greatscottgadgets/daisho/sw/fpga/common/usb3/usb3_crc.v

//
// usb 3.0 crc assortment
//
// Copyright (C) 2009 OutputLogic.com
// Reformatting / adaptation by Marshall H., 2013
// This source file may be used and distributed without restriction
// provided that this copyright statement is not removed from the file
// and that any derivative work contains the original copyright notice
// and the associated disclaimer.
//
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


//
// CRC-5 for Command Words, Link Control Word
//
module usb3_crc_cw(

input 	wire	[10:0] 	di,
output 	wire	[4:0] 	crc_out

);

// reverse input
wire	[10:0]	d = { 	di[0], di[1], di[2], di[3], di[4], 
						di[5], di[6], di[7], di[8], di[9], 
						di[10] };
wire	[4:0]	c = 5'h1F;						
wire	[4:0]	q = {	^d[10:9] ^ ^d[6:5] ^ d[3] ^ d[0] ^ c[0] ^ ^c[4:3],
						d[10] ^ ^d[7:6] ^ d[4] ^ d[1] ^ ^c[1:0] ^ c[4],
						^d[10:7] ^ d[6] ^ ^d[3:2] ^ d[0] ^ ^c[4:0],
						^d[10:7] ^^ d[4:3] ^ d[1] ^ ^c[4:1],
						^d[10:8] ^ ^d[5:4] ^ d[2] ^ ^c[4:2]	};
assign	crc_out = ~q;
	
endmodule



//
// CRC-16 for Header Packets
//
module usb3_crc_hp(

input	wire	[31:0] 	di,
input	wire			crc_en,
output	wire	[15:0] 	crc_out,
input	wire			rst,
input	wire			clk

);

reg [15:0]	q;
wire [15:0]	c;
wire [31:0] d = {	di[0 ],di[1 ],di[2 ],di[3 ],di[4 ],di[5 ],di[6 ],di[7],
					di[8 ],di[9 ],di[10],di[11],di[12],di[13],di[14],di[15],
					di[16],di[17],di[18],di[19],di[20],di[21],di[22],di[23],
					di[24],di[25],di[26],di[27],di[28],di[29],di[30],di[31]};
assign crc_out = ~{	q[0], q[1], q[2], q[3], q[4], q[5], q[6], q[7], 
					q[8], q[9], q[10],q[11],q[12],q[13],q[14],q[15]};

assign	c[0] = q[4] ^ q[5] ^ q[7] ^ q[10] ^ q[12] ^ q[13] ^ q[15] ^ d[0] ^ d[4] ^ d[8] ^ d[12] ^ d[13] ^ d[15] ^ d[20] ^ d[21] ^ d[23] ^ d[26] ^ d[28] ^ d[29] ^ d[31];
assign	c[1] = q[0] ^ q[4] ^ q[6] ^ q[7] ^ q[8] ^ q[10] ^ q[11] ^ q[12] ^ q[14] ^ q[15] ^ d[0] ^ d[1] ^ d[4] ^ d[5] ^ d[8] ^ d[9] ^ d[12] ^ d[14] ^ d[15] ^ d[16] ^ d[20] ^ d[22] ^ d[23] ^ d[24] ^ d[26] ^ d[27] ^ d[28] ^ d[30] ^ d[31];
assign	c[2] = q[0] ^ q[1] ^ q[5] ^ q[7] ^ q[8] ^ q[9] ^ q[11] ^ q[12] ^ q[13] ^ q[15] ^ d[1] ^ d[2] ^ d[5] ^ d[6] ^ d[9] ^ d[10] ^ d[13] ^ d[15] ^ d[16] ^ d[17] ^ d[21] ^ d[23] ^ d[24] ^ d[25] ^ d[27] ^ d[28] ^ d[29] ^ d[31];
assign	c[3] = q[0] ^ q[1] ^ q[2] ^ q[4] ^ q[5] ^ q[6] ^ q[7] ^ q[8] ^ q[9] ^ q[14] ^ q[15] ^ d[0] ^ d[2] ^ d[3] ^ d[4] ^ d[6] ^ d[7] ^ d[8] ^ d[10] ^ d[11] ^ d[12] ^ d[13] ^ d[14] ^ d[15] ^ d[16] ^ d[17] ^ d[18] ^ d[20] ^ d[21] ^ d[22] ^ d[23] ^ d[24] ^ d[25] ^ d[30] ^ d[31];
assign	c[4] = q[0] ^ q[1] ^ q[2] ^ q[3] ^ q[5] ^ q[6] ^ q[7] ^ q[8] ^ q[9] ^ q[10] ^ q[15] ^ d[1] ^ d[3] ^ d[4] ^ d[5] ^ d[7] ^ d[8] ^ d[9] ^ d[11] ^ d[12] ^ d[13] ^ d[14] ^ d[15] ^ d[16] ^ d[17] ^ d[18] ^ d[19] ^ d[21] ^ d[22] ^ d[23] ^ d[24] ^ d[25] ^ d[26] ^ d[31];
assign	c[5] = q[0] ^ q[1] ^ q[2] ^ q[3] ^ q[4] ^ q[6] ^ q[7] ^ q[8] ^ q[9] ^ q[10] ^ q[11] ^ d[2] ^ d[4] ^ d[5] ^ d[6] ^ d[8] ^ d[9] ^ d[10] ^ d[12] ^ d[13] ^ d[14] ^ d[15] ^ d[16] ^ d[17] ^ d[18] ^ d[19] ^ d[20] ^ d[22] ^ d[23] ^ d[24] ^ d[25] ^ d[26] ^ d[27];
assign	c[6] = q[0] ^ q[1] ^ q[2] ^ q[3] ^ q[4] ^ q[5] ^ q[7] ^ q[8] ^ q[9] ^ q[10] ^ q[11] ^ q[12] ^ d[3] ^ d[5] ^ d[6] ^ d[7] ^ d[9] ^ d[10] ^ d[11] ^ d[13] ^ d[14] ^ d[15] ^ d[16] ^ d[17] ^ d[18] ^ d[19] ^ d[20] ^ d[21] ^ d[23] ^ d[24] ^ d[25] ^ d[26] ^ d[27] ^ d[28];
assign	c[7] = q[0] ^ q[1] ^ q[2] ^ q[3] ^ q[4] ^ q[5] ^ q[6] ^ q[8] ^ q[9] ^ q[10] ^ q[11] ^ q[12] ^ q[13] ^ d[4] ^ d[6] ^ d[7] ^ d[8] ^ d[10] ^ d[11] ^ d[12] ^ d[14] ^ d[15] ^ d[16] ^ d[17] ^ d[18] ^ d[19] ^ d[20] ^ d[21] ^ d[22] ^ d[24] ^ d[25] ^ d[26] ^ d[27] ^ d[28] ^ d[29];
assign	c[8] = q[0] ^ q[1] ^ q[2] ^ q[3] ^ q[4] ^ q[5] ^ q[6] ^ q[7] ^ q[9] ^ q[10] ^ q[11] ^ q[12] ^ q[13] ^ q[14] ^ d[5] ^ d[7] ^ d[8] ^ d[9] ^ d[11] ^ d[12] ^ d[13] ^ d[15] ^ d[16] ^ d[17] ^ d[18] ^ d[19] ^ d[20] ^ d[21] ^ d[22] ^ d[23] ^ d[25] ^ d[26] ^ d[27] ^ d[28] ^ d[29] ^ d[30];
assign	c[9] = q[0] ^ q[1] ^ q[2] ^ q[3] ^ q[4] ^ q[5] ^ q[6] ^ q[7] ^ q[8] ^ q[10] ^ q[11] ^ q[12] ^ q[13] ^ q[14] ^ q[15] ^ d[6] ^ d[8] ^ d[9] ^ d[10] ^ d[12] ^ d[13] ^ d[14] ^ d[16] ^ d[17] ^ d[18] ^ d[19] ^ d[20] ^ d[21] ^ d[22] ^ d[23] ^ d[24] ^ d[26] ^ d[27] ^ d[28] ^ d[29] ^ d[30] ^ d[31];
assign	c[10] = q[1] ^ q[2] ^ q[3] ^ q[4] ^ q[5] ^ q[6] ^ q[7] ^ q[8] ^ q[9] ^ q[11] ^ q[12] ^ q[13] ^ q[14] ^ q[15] ^ d[7] ^ d[9] ^ d[10] ^ d[11] ^ d[13] ^ d[14] ^ d[15] ^ d[17] ^ d[18] ^ d[19] ^ d[20] ^ d[21] ^ d[22] ^ d[23] ^ d[24] ^ d[25] ^ d[27] ^ d[28] ^ d[29] ^ d[30] ^ d[31]; 
assign  c[11] = q[0] ^ q[2] ^ q[3] ^ q[4] ^ q[5] ^ q[6] ^ q[7] ^ q[8] ^ q[9] ^ q[10] ^ q[12] ^ q[13] ^ q[14] ^ q[15] ^ d[8] ^ d[10] ^ d[11] ^ d[12] ^ d[14] ^ d[15] ^ d[16] ^ d[18] ^ d[19] ^ d[20] ^ d[21] ^ d[22] ^ d[23] ^ d[24] ^ d[25] ^ d[26] ^ d[28] ^ d[29] ^ d[30] ^ d[31];
assign	c[12] = q[0] ^ q[1] ^ q[3] ^ q[6] ^ q[8] ^ q[9] ^ q[11] ^ q[12] ^ q[14] ^ d[0] ^ d[4] ^ d[8] ^ d[9] ^ d[11] ^ d[16] ^ d[17] ^ d[19] ^ d[22] ^ d[24] ^ d[25] ^ d[27] ^ d[28] ^ d[30];
assign	c[13] = q[1] ^ q[2] ^ q[4] ^ q[7] ^ q[9] ^ q[10] ^ q[12] ^ q[13] ^ q[15] ^ d[1] ^ d[5] ^ d[9] ^ d[10] ^ d[12] ^ d[17] ^ d[18] ^ d[20] ^ d[23] ^ d[25] ^ d[26] ^ d[28] ^ d[29] ^ d[31];
assign	c[14] = q[2] ^ q[3] ^ q[5] ^ q[8] ^ q[10] ^ q[11] ^ q[13] ^ q[14] ^ d[2] ^ d[6] ^ d[10] ^ d[11] ^ d[13] ^ d[18] ^ d[19] ^ d[21] ^ d[24] ^ d[26] ^ d[27] ^ d[29] ^ d[30];
assign	c[15] = q[3] ^ q[4] ^ q[6] ^ q[9] ^ q[11] ^ q[12] ^ q[14] ^ q[15] ^ d[3] ^ d[7] ^ d[11] ^ d[12] ^ d[14] ^ d[19] ^ d[20] ^ d[22] ^ d[25] ^ d[27] ^ d[28] ^ d[30] ^ d[31];

always @(posedge clk, posedge rst) begin
	if(rst) begin
		q <= {16{1'b1}};
	end
	else begin
		q <= crc_en ? c : q;
	end
end

endmodule



//
// CRC-32 for Data Packet Payloads
//
module usb3_crc_dpp32(

input 	wire	[31:0]	di,
output	wire	[31:0]	lfsr_q,
input 	wire			crc_en,
output	wire	[31:0]	crc_out,
input	wire			rst,
input	wire			clk

);

reg [31:0] q;

wire [31:0]	c;
wire [31:0] d = {	di[0 ],di[1 ],di[2 ],di[3 ],di[4 ],di[5 ],di[6 ],di[7],
					di[8 ],di[9 ],di[10],di[11],di[12],di[13],di[14],di[15],
					di[16],di[17],di[18],di[19],di[20],di[21],di[22],di[23],
					di[24],di[25],di[26],di[27],di[28],di[29],di[30],di[31]};
						
assign lfsr_q = q;
assign crc_out = ~{	q[0],  q[1],  q[2],  q[3],  q[4],  q[5],  q[6],  q[7], 
					q[8],  q[9],  q[10], q[11], q[12], q[13], q[14], q[15],
					q[16], q[17], q[18], q[19], q[20], q[21], q[22], q[23], 
					q[24], q[25], q[26], q[27], q[28], q[29], q[30], q[31]};

assign	c[0] = q[0] ^ q[6] ^ q[9] ^ q[10] ^ q[12] ^ q[16] ^ q[24] ^ q[25] ^ q[26] ^ q[28] ^ q[29] ^ q[30] ^ q[31] ^ d[0] ^ d[6] ^ d[9] ^ d[10] ^ d[12] ^ d[16] ^ d[24] ^ d[25] ^ d[26] ^ d[28] ^ d[29] ^ d[30] ^ d[31];
assign	c[1] = q[0] ^ q[1] ^ q[6] ^ q[7] ^ q[9] ^ q[11] ^ q[12] ^ q[13] ^ q[16] ^ q[17] ^ q[24] ^ q[27] ^ q[28] ^ d[0] ^ d[1] ^ d[6] ^ d[7] ^ d[9] ^ d[11] ^ d[12] ^ d[13] ^ d[16] ^ d[17] ^ d[24] ^ d[27] ^ d[28];
assign	c[2] = q[0] ^ q[1] ^ q[2] ^ q[6] ^ q[7] ^ q[8] ^ q[9] ^ q[13] ^ q[14] ^ q[16] ^ q[17] ^ q[18] ^ q[24] ^ q[26] ^ q[30] ^ q[31] ^ d[0] ^ d[1] ^ d[2] ^ d[6] ^ d[7] ^ d[8] ^ d[9] ^ d[13] ^ d[14] ^ d[16] ^ d[17] ^ d[18] ^ d[24] ^ d[26] ^ d[30] ^ d[31];
assign	c[3] = q[1] ^ q[2] ^ q[3] ^ q[7] ^ q[8] ^ q[9] ^ q[10] ^ q[14] ^ q[15] ^ q[17] ^ q[18] ^ q[19] ^ q[25] ^ q[27] ^ q[31] ^ d[1] ^ d[2] ^ d[3] ^ d[7] ^ d[8] ^ d[9] ^ d[10] ^ d[14] ^ d[15] ^ d[17] ^ d[18] ^ d[19] ^ d[25] ^ d[27] ^ d[31];
assign	c[4] = q[0] ^ q[2] ^ q[3] ^ q[4] ^ q[6] ^ q[8] ^ q[11] ^ q[12] ^ q[15] ^ q[18] ^ q[19] ^ q[20] ^ q[24] ^ q[25] ^ q[29] ^ q[30] ^ q[31] ^ d[0] ^ d[2] ^ d[3] ^ d[4] ^ d[6] ^ d[8] ^ d[11] ^ d[12] ^ d[15] ^ d[18] ^ d[19] ^ d[20] ^ d[24] ^ d[25] ^ d[29] ^ d[30] ^ d[31];
assign	c[5] = q[0] ^ q[1] ^ q[3] ^ q[4] ^ q[5] ^ q[6] ^ q[7] ^ q[10] ^ q[13] ^ q[19] ^ q[20] ^ q[21] ^ q[24] ^ q[28] ^ q[29] ^ d[0] ^ d[1] ^ d[3] ^ d[4] ^ d[5] ^ d[6] ^ d[7] ^ d[10] ^ d[13] ^ d[19] ^ d[20] ^ d[21] ^ d[24] ^ d[28] ^ d[29];
assign	c[6] = q[1] ^ q[2] ^ q[4] ^ q[5] ^ q[6] ^ q[7] ^ q[8] ^ q[11] ^ q[14] ^ q[20] ^ q[21] ^ q[22] ^ q[25] ^ q[29] ^ q[30] ^ d[1] ^ d[2] ^ d[4] ^ d[5] ^ d[6] ^ d[7] ^ d[8] ^ d[11] ^ d[14] ^ d[20] ^ d[21] ^ d[22] ^ d[25] ^ d[29] ^ d[30];
assign	c[7] = q[0] ^ q[2] ^ q[3] ^ q[5] ^ q[7] ^ q[8] ^ q[10] ^ q[15] ^ q[16] ^ q[21] ^ q[22] ^ q[23] ^ q[24] ^ q[25] ^ q[28] ^ q[29] ^ d[0] ^ d[2] ^ d[3] ^ d[5] ^ d[7] ^ d[8] ^ d[10] ^ d[15] ^ d[16] ^ d[21] ^ d[22] ^ d[23] ^ d[24] ^ d[25] ^ d[28] ^ d[29];
assign	c[8] = q[0] ^ q[1] ^ q[3] ^ q[4] ^ q[8] ^ q[10] ^ q[11] ^ q[12] ^ q[17] ^ q[22] ^ q[23] ^ q[28] ^ q[31] ^ d[0] ^ d[1] ^ d[3] ^ d[4] ^ d[8] ^ d[10] ^ d[11] ^ d[12] ^ d[17] ^ d[22] ^ d[23] ^ d[28] ^ d[31];
assign	c[9] = q[1] ^ q[2] ^ q[4] ^ q[5] ^ q[9] ^ q[11] ^ q[12] ^ q[13] ^ q[18] ^ q[23] ^ q[24] ^ q[29] ^ d[1] ^ d[2] ^ d[4] ^ d[5] ^ d[9] ^ d[11] ^ d[12] ^ d[13] ^ d[18] ^ d[23] ^ d[24] ^ d[29];
assign	c[10] = q[0] ^ q[2] ^ q[3] ^ q[5] ^ q[9] ^ q[13] ^ q[14] ^ q[16] ^ q[19] ^ q[26] ^ q[28] ^ q[29] ^ q[31] ^ d[0] ^ d[2] ^ d[3] ^ d[5] ^ d[9] ^ d[13] ^ d[14] ^ d[16] ^ d[19] ^ d[26] ^ d[28] ^ d[29] ^ d[31];
assign	c[11] = q[0] ^ q[1] ^ q[3] ^ q[4] ^ q[9] ^ q[12] ^ q[14] ^ q[15] ^ q[16] ^ q[17] ^ q[20] ^ q[24] ^ q[25] ^ q[26] ^ q[27] ^ q[28] ^ q[31] ^ d[0] ^ d[1] ^ d[3] ^ d[4] ^ d[9] ^ d[12] ^ d[14] ^ d[15] ^ d[16] ^ d[17] ^ d[20] ^ d[24] ^ d[25] ^ d[26] ^ d[27] ^ d[28] ^ d[31];
assign	c[12] = q[0] ^ q[1] ^ q[2] ^ q[4] ^ q[5] ^ q[6] ^ q[9] ^ q[12] ^ q[13] ^ q[15] ^ q[17] ^ q[18] ^ q[21] ^ q[24] ^ q[27] ^ q[30] ^ q[31] ^ d[0] ^ d[1] ^ d[2] ^ d[4] ^ d[5] ^ d[6] ^ d[9] ^ d[12] ^ d[13] ^ d[15] ^ d[17] ^ d[18] ^ d[21] ^ d[24] ^ d[27] ^ d[30] ^ d[31];
assign	c[13] = q[1] ^ q[2] ^ q[3] ^ q[5] ^ q[6] ^ q[7] ^ q[10] ^ q[13] ^ q[14] ^ q[16] ^ q[18] ^ q[19] ^ q[22] ^ q[25] ^ q[28] ^ q[31] ^ d[1] ^ d[2] ^ d[3] ^ d[5] ^ d[6] ^ d[7] ^ d[10] ^ d[13] ^ d[14] ^ d[16] ^ d[18] ^ d[19] ^ d[22] ^ d[25] ^ d[28] ^ d[31];
assign	c[14] = q[2] ^ q[3] ^ q[4] ^ q[6] ^ q[7] ^ q[8] ^ q[11] ^ q[14] ^ q[15] ^ q[17] ^ q[19] ^ q[20] ^ q[23] ^ q[26] ^ q[29] ^ d[2] ^ d[3] ^ d[4] ^ d[6] ^ d[7] ^ d[8] ^ d[11] ^ d[14] ^ d[15] ^ d[17] ^ d[19] ^ d[20] ^ d[23] ^ d[26] ^ d[29];
assign	c[15] = q[3] ^ q[4] ^ q[5] ^ q[7] ^ q[8] ^ q[9] ^ q[12] ^ q[15] ^ q[16] ^ q[18] ^ q[20] ^ q[21] ^ q[24] ^ q[27] ^ q[30] ^ d[3] ^ d[4] ^ d[5] ^ d[7] ^ d[8] ^ d[9] ^ d[12] ^ d[15] ^ d[16] ^ d[18] ^ d[20] ^ d[21] ^ d[24] ^ d[27] ^ d[30];
assign	c[16] = q[0] ^ q[4] ^ q[5] ^ q[8] ^ q[12] ^ q[13] ^ q[17] ^ q[19] ^ q[21] ^ q[22] ^ q[24] ^ q[26] ^ q[29] ^ q[30] ^ d[0] ^ d[4] ^ d[5] ^ d[8] ^ d[12] ^ d[13] ^ d[17] ^ d[19] ^ d[21] ^ d[22] ^ d[24] ^ d[26] ^ d[29] ^ d[30];
assign	c[17] = q[1] ^ q[5] ^ q[6] ^ q[9] ^ q[13] ^ q[14] ^ q[18] ^ q[20] ^ q[22] ^ q[23] ^ q[25] ^ q[27] ^ q[30] ^ q[31] ^ d[1] ^ d[5] ^ d[6] ^ d[9] ^ d[13] ^ d[14] ^ d[18] ^ d[20] ^ d[22] ^ d[23] ^ d[25] ^ d[27] ^ d[30] ^ d[31];
assign	c[18] = q[2] ^ q[6] ^ q[7] ^ q[10] ^ q[14] ^ q[15] ^ q[19] ^ q[21] ^ q[23] ^ q[24] ^ q[26] ^ q[28] ^ q[31] ^ d[2] ^ d[6] ^ d[7] ^ d[10] ^ d[14] ^ d[15] ^ d[19] ^ d[21] ^ d[23] ^ d[24] ^ d[26] ^ d[28] ^ d[31];
assign	c[19] = q[3] ^ q[7] ^ q[8] ^ q[11] ^ q[15] ^ q[16] ^ q[20] ^ q[22] ^ q[24] ^ q[25] ^ q[27] ^ q[29] ^ d[3] ^ d[7] ^ d[8] ^ d[11] ^ d[15] ^ d[16] ^ d[20] ^ d[22] ^ d[24] ^ d[25] ^ d[27] ^ d[29];
assign	c[20] = q[4] ^ q[8] ^ q[9] ^ q[12] ^ q[16] ^ q[17] ^ q[21] ^ q[23] ^ q[25] ^ q[26] ^ q[28] ^ q[30] ^ d[4] ^ d[8] ^ d[9] ^ d[12] ^ d[16] ^ d[17] ^ d[21] ^ d[23] ^ d[25] ^ d[26] ^ d[28] ^ d[30];
assign	c[21] = q[5] ^ q[9] ^ q[10] ^ q[13] ^ q[17] ^ q[18] ^ q[22] ^ q[24] ^ q[26] ^ q[27] ^ q[29] ^ q[31] ^ d[5] ^ d[9] ^ d[10] ^ d[13] ^ d[17] ^ d[18] ^ d[22] ^ d[24] ^ d[26] ^ d[27] ^ d[29] ^ d[31];
assign	c[22] = q[0] ^ q[9] ^ q[11] ^ q[12] ^ q[14] ^ q[16] ^ q[18] ^ q[19] ^ q[23] ^ q[24] ^ q[26] ^ q[27] ^ q[29] ^ q[31] ^ d[0] ^ d[9] ^ d[11] ^ d[12] ^ d[14] ^ d[16] ^ d[18] ^ d[19] ^ d[23] ^ d[24] ^ d[26] ^ d[27] ^ d[29] ^ d[31];
assign	c[23] = q[0] ^ q[1] ^ q[6] ^ q[9] ^ q[13] ^ q[15] ^ q[16] ^ q[17] ^ q[19] ^ q[20] ^ q[26] ^ q[27] ^ q[29] ^ q[31] ^ d[0] ^ d[1] ^ d[6] ^ d[9] ^ d[13] ^ d[15] ^ d[16] ^ d[17] ^ d[19] ^ d[20] ^ d[26] ^ d[27] ^ d[29] ^ d[31];
assign	c[24] = q[1] ^ q[2] ^ q[7] ^ q[10] ^ q[14] ^ q[16] ^ q[17] ^ q[18] ^ q[20] ^ q[21] ^ q[27] ^ q[28] ^ q[30] ^ d[1] ^ d[2] ^ d[7] ^ d[10] ^ d[14] ^ d[16] ^ d[17] ^ d[18] ^ d[20] ^ d[21] ^ d[27] ^ d[28] ^ d[30];
assign	c[25] = q[2] ^ q[3] ^ q[8] ^ q[11] ^ q[15] ^ q[17] ^ q[18] ^ q[19] ^ q[21] ^ q[22] ^ q[28] ^ q[29] ^ q[31] ^ d[2] ^ d[3] ^ d[8] ^ d[11] ^ d[15] ^ d[17] ^ d[18] ^ d[19] ^ d[21] ^ d[22] ^ d[28] ^ d[29] ^ d[31];
assign	c[26] = q[0] ^ q[3] ^ q[4] ^ q[6] ^ q[10] ^ q[18] ^ q[19] ^ q[20] ^ q[22] ^ q[23] ^ q[24] ^ q[25] ^ q[26] ^ q[28] ^ q[31] ^ d[0] ^ d[3] ^ d[4] ^ d[6] ^ d[10] ^ d[18] ^ d[19] ^ d[20] ^ d[22] ^ d[23] ^ d[24] ^ d[25] ^ d[26] ^ d[28] ^ d[31];
assign	c[27] = q[1] ^ q[4] ^ q[5] ^ q[7] ^ q[11] ^ q[19] ^ q[20] ^ q[21] ^ q[23] ^ q[24] ^ q[25] ^ q[26] ^ q[27] ^ q[29] ^ d[1] ^ d[4] ^ d[5] ^ d[7] ^ d[11] ^ d[19] ^ d[20] ^ d[21] ^ d[23] ^ d[24] ^ d[25] ^ d[26] ^ d[27] ^ d[29];
assign	c[28] = q[2] ^ q[5] ^ q[6] ^ q[8] ^ q[12] ^ q[20] ^ q[21] ^ q[22] ^ q[24] ^ q[25] ^ q[26] ^ q[27] ^ q[28] ^ q[30] ^ d[2] ^ d[5] ^ d[6] ^ d[8] ^ d[12] ^ d[20] ^ d[21] ^ d[22] ^ d[24] ^ d[25] ^ d[26] ^ d[27] ^ d[28] ^ d[30];
assign	c[29] = q[3] ^ q[6] ^ q[7] ^ q[9] ^ q[13] ^ q[21] ^ q[22] ^ q[23] ^ q[25] ^ q[26] ^ q[27] ^ q[28] ^ q[29] ^ q[31] ^ d[3] ^ d[6] ^ d[7] ^ d[9] ^ d[13] ^ d[21] ^ d[22] ^ d[23] ^ d[25] ^ d[26] ^ d[27] ^ d[28] ^ d[29] ^ d[31];
assign	c[30] = q[4] ^ q[7] ^ q[8] ^ q[10] ^ q[14] ^ q[22] ^ q[23] ^ q[24] ^ q[26] ^ q[27] ^ q[28] ^ q[29] ^ q[30] ^ d[4] ^ d[7] ^ d[8] ^ d[10] ^ d[14] ^ d[22] ^ d[23] ^ d[24] ^ d[26] ^ d[27] ^ d[28] ^ d[29] ^ d[30];
assign	c[31] = q[5] ^ q[8] ^ q[9] ^ q[11] ^ q[15] ^ q[23] ^ q[24] ^ q[25] ^ q[27] ^ q[28] ^ q[29] ^ q[30] ^ q[31] ^ d[5] ^ d[8] ^ d[9] ^ d[11] ^ d[15] ^ d[23] ^ d[24] ^ d[25] ^ d[27] ^ d[28] ^ d[29] ^ d[30] ^ d[31];

always @(posedge clk, posedge rst) begin
	if(rst) begin
		q <= {32{1'b1}};
	end
	else begin
		q <= crc_en ? c : q;
	end
end

endmodule



module usb3_crc_dpp24 (

input 	wire	[23:0]	di,
input	wire	[31:0]	q,
output	wire	[31:0]	crc_out,
input	wire			rst,
input	wire			clk

);

wire [31:0]	c;
wire [23:0] d = {	di[0 ],di[1 ],di[2 ],di[3 ],di[4 ],di[5 ],di[6 ],di[7],
					di[8 ],di[9 ],di[10],di[11],di[12],di[13],di[14],di[15],
					di[16],di[17],di[18],di[19],di[20],di[21],di[22],di[23]};

assign crc_out = ~{	c[0],  c[1],  c[2],  c[3],  c[4],  c[5],  c[6],  c[7], 
					c[8],  c[9],  c[10], c[11], c[12], c[13], c[14], c[15],
					c[16], c[17], c[18], c[19], c[20], c[21], c[22], c[23], 
					c[24], c[25], c[26], c[27], c[28], c[29], c[30], c[31]};

assign	c[0] = q[8] ^ q[14] ^ q[17] ^ q[18] ^ q[20] ^ q[24] ^ d[0] ^ d[6] ^ d[9] ^ d[10] ^ d[12] ^ d[16];
assign	c[1] = q[8] ^ q[9] ^ q[14] ^ q[15] ^ q[17] ^ q[19] ^ q[20] ^ q[21] ^ q[24] ^ q[25] ^ d[0] ^ d[1] ^ d[6] ^ d[7] ^ d[9] ^ d[11] ^ d[12] ^ d[13] ^ d[16] ^ d[17];
assign	c[2] = q[8] ^ q[9] ^ q[10] ^ q[14] ^ q[15] ^ q[16] ^ q[17] ^ q[21] ^ q[22] ^ q[24] ^ q[25] ^ q[26] ^ d[0] ^ d[1] ^ d[2] ^ d[6] ^ d[7] ^ d[8] ^ d[9] ^ d[13] ^ d[14] ^ d[16] ^ d[17] ^ d[18];
assign	c[3] = q[9] ^ q[10] ^ q[11] ^ q[15] ^ q[16] ^ q[17] ^ q[18] ^ q[22] ^ q[23] ^ q[25] ^ q[26] ^ q[27] ^ d[1] ^ d[2] ^ d[3] ^ d[7] ^ d[8] ^ d[9] ^ d[10] ^ d[14] ^ d[15] ^ d[17] ^ d[18] ^ d[19];
assign	c[4] = q[8] ^ q[10] ^ q[11] ^ q[12] ^ q[14] ^ q[16] ^ q[19] ^ q[20] ^ q[23] ^ q[26] ^ q[27] ^ q[28] ^ d[0] ^ d[2] ^ d[3] ^ d[4] ^ d[6] ^ d[8] ^ d[11] ^ d[12] ^ d[15] ^ d[18] ^ d[19] ^ d[20];
assign	c[5] = q[8] ^ q[9] ^ q[11] ^ q[12] ^ q[13] ^ q[14] ^ q[15] ^ q[18] ^ q[21] ^ q[27] ^ q[28] ^ q[29] ^ d[0] ^ d[1] ^ d[3] ^ d[4] ^ d[5] ^ d[6] ^ d[7] ^ d[10] ^ d[13] ^ d[19] ^ d[20] ^ d[21];
assign	c[6] = q[9] ^ q[10] ^ q[12] ^ q[13] ^ q[14] ^ q[15] ^ q[16] ^ q[19] ^ q[22] ^ q[28] ^ q[29] ^ q[30] ^ d[1] ^ d[2] ^ d[4] ^ d[5] ^ d[6] ^ d[7] ^ d[8] ^ d[11] ^ d[14] ^ d[20] ^ d[21] ^ d[22];
assign	c[7] = q[8] ^ q[10] ^ q[11] ^ q[13] ^ q[15] ^ q[16] ^ q[18] ^ q[23] ^ q[24] ^ q[29] ^ q[30] ^ q[31] ^ d[0] ^ d[2] ^ d[3] ^ d[5] ^ d[7] ^ d[8] ^ d[10] ^ d[15] ^ d[16] ^ d[21] ^ d[22] ^ d[23];
assign	c[8] = q[8] ^ q[9] ^ q[11] ^ q[12] ^ q[16] ^ q[18] ^ q[19] ^ q[20] ^ q[25] ^ q[30] ^ q[31] ^ d[0] ^ d[1] ^ d[3] ^ d[4] ^ d[8] ^ d[10] ^ d[11] ^ d[12] ^ d[17] ^ d[22] ^ d[23];
assign	c[9] = q[9] ^ q[10] ^ q[12] ^ q[13] ^ q[17] ^ q[19] ^ q[20] ^ q[21] ^ q[26] ^ q[31] ^ d[1] ^ d[2] ^ d[4] ^ d[5] ^ d[9] ^ d[11] ^ d[12] ^ d[13] ^ d[18] ^ d[23];
assign	c[10] = q[8] ^ q[10] ^ q[11] ^ q[13] ^ q[17] ^ q[21] ^ q[22] ^ q[24] ^ q[27] ^ d[0] ^ d[2] ^ d[3] ^ d[5] ^ d[9] ^ d[13] ^ d[14] ^ d[16] ^ d[19];
assign	c[11] = q[8] ^ q[9] ^ q[11] ^ q[12] ^ q[17] ^ q[20] ^ q[22] ^ q[23] ^ q[24] ^ q[25] ^ q[28] ^ d[0] ^ d[1] ^ d[3] ^ d[4] ^ d[9] ^ d[12] ^ d[14] ^ d[15] ^ d[16] ^ d[17] ^ d[20];
assign	c[12] = q[8] ^ q[9] ^ q[10] ^ q[12] ^ q[13] ^ q[14] ^ q[17] ^ q[20] ^ q[21] ^ q[23] ^ q[25] ^ q[26] ^ q[29] ^ d[0] ^ d[1] ^ d[2] ^ d[4] ^ d[5] ^ d[6] ^ d[9] ^ d[12] ^ d[13] ^ d[15] ^ d[17] ^ d[18] ^ d[21];
assign	c[13] = q[9] ^ q[10] ^ q[11] ^ q[13] ^ q[14] ^ q[15] ^ q[18] ^ q[21] ^ q[22] ^ q[24] ^ q[26] ^ q[27] ^ q[30] ^ d[1] ^ d[2] ^ d[3] ^ d[5] ^ d[6] ^ d[7] ^ d[10] ^ d[13] ^ d[14] ^ d[16] ^ d[18] ^ d[19] ^ d[22];
assign	c[14] = q[10] ^ q[11] ^ q[12] ^ q[14] ^ q[15] ^ q[16] ^ q[19] ^ q[22] ^ q[23] ^ q[25] ^ q[27] ^ q[28] ^ q[31] ^ d[2] ^ d[3] ^ d[4] ^ d[6] ^ d[7] ^ d[8] ^ d[11] ^ d[14] ^ d[15] ^ d[17] ^ d[19] ^ d[20] ^ d[23];
assign	c[15] = q[11] ^ q[12] ^ q[13] ^ q[15] ^ q[16] ^ q[17] ^ q[20] ^ q[23] ^ q[24] ^ q[26] ^ q[28] ^ q[29] ^ d[3] ^ d[4] ^ d[5] ^ d[7] ^ d[8] ^ d[9] ^ d[12] ^ d[15] ^ d[16] ^ d[18] ^ d[20] ^ d[21];
assign	c[16] = q[8] ^ q[12] ^ q[13] ^ q[16] ^ q[20] ^ q[21] ^ q[25] ^ q[27] ^ q[29] ^ q[30] ^ d[0] ^ d[4] ^ d[5] ^ d[8] ^ d[12] ^ d[13] ^ d[17] ^ d[19] ^ d[21] ^ d[22];
assign	c[17] = q[9] ^ q[13] ^ q[14] ^ q[17] ^ q[21] ^ q[22] ^ q[26] ^ q[28] ^ q[30] ^ q[31] ^ d[1] ^ d[5] ^ d[6] ^ d[9] ^ d[13] ^ d[14] ^ d[18] ^ d[20] ^ d[22] ^ d[23];
assign	c[18] = q[10] ^ q[14] ^ q[15] ^ q[18] ^ q[22] ^ q[23] ^ q[27] ^ q[29] ^ q[31] ^ d[2] ^ d[6] ^ d[7] ^ d[10] ^ d[14] ^ d[15] ^ d[19] ^ d[21] ^ d[23];
assign	c[19] = q[11] ^ q[15] ^ q[16] ^ q[19] ^ q[23] ^ q[24] ^ q[28] ^ q[30] ^ d[3] ^ d[7] ^ d[8] ^ d[11] ^ d[15] ^ d[16] ^ d[20] ^ d[22];
assign	c[20] = q[12] ^ q[16] ^ q[17] ^ q[20] ^ q[24] ^ q[25] ^ q[29] ^ q[31] ^ d[4] ^ d[8] ^ d[9] ^ d[12] ^ d[16] ^ d[17] ^ d[21] ^ d[23];
assign	c[21] = q[13] ^ q[17] ^ q[18] ^ q[21] ^ q[25] ^ q[26] ^ q[30] ^ d[5] ^ d[9] ^ d[10] ^ d[13] ^ d[17] ^ d[18] ^ d[22];
assign	c[22] = q[8] ^ q[17] ^ q[19] ^ q[20] ^ q[22] ^ q[24] ^ q[26] ^ q[27] ^ q[31] ^ d[0] ^ d[9] ^ d[11] ^ d[12] ^ d[14] ^ d[16] ^ d[18] ^ d[19] ^ d[23];
assign	c[23] = q[8] ^ q[9] ^ q[14] ^ q[17] ^ q[21] ^ q[23] ^ q[24] ^ q[25] ^ q[27] ^ q[28] ^ d[0] ^ d[1] ^ d[6] ^ d[9] ^ d[13] ^ d[15] ^ d[16] ^ d[17] ^ d[19] ^ d[20];
assign	c[24] = q[0] ^ q[9] ^ q[10] ^ q[15] ^ q[18] ^ q[22] ^ q[24] ^ q[25] ^ q[26] ^ q[28] ^ q[29] ^ d[1] ^ d[2] ^ d[7] ^ d[10] ^ d[14] ^ d[16] ^ d[17] ^ d[18] ^ d[20] ^ d[21];
assign	c[25] = q[1] ^ q[10] ^ q[11] ^ q[16] ^ q[19] ^ q[23] ^ q[25] ^ q[26] ^ q[27] ^ q[29] ^ q[30] ^ d[2] ^ d[3] ^ d[8] ^ d[11] ^ d[15] ^ d[17] ^ d[18] ^ d[19] ^ d[21] ^ d[22];
assign	c[26] = q[2] ^ q[8] ^ q[11] ^ q[12] ^ q[14] ^ q[18] ^ q[26] ^ q[27] ^ q[28] ^ q[30] ^ q[31] ^ d[0] ^ d[3] ^ d[4] ^ d[6] ^ d[10] ^ d[18] ^ d[19] ^ d[20] ^ d[22] ^ d[23];
assign	c[27] = q[3] ^ q[9] ^ q[12] ^ q[13] ^ q[15] ^ q[19] ^ q[27] ^ q[28] ^ q[29] ^ q[31] ^ d[1] ^ d[4] ^ d[5] ^ d[7] ^ d[11] ^ d[19] ^ d[20] ^ d[21] ^ d[23];
assign	c[28] = q[4] ^ q[10] ^ q[13] ^ q[14] ^ q[16] ^ q[20] ^ q[28] ^ q[29] ^ q[30] ^ d[2] ^ d[5] ^ d[6] ^ d[8] ^ d[12] ^ d[20] ^ d[21] ^ d[22];
assign	c[29] = q[5] ^ q[11] ^ q[14] ^ q[15] ^ q[17] ^ q[21] ^ q[29] ^ q[30] ^ q[31] ^ d[3] ^ d[6] ^ d[7] ^ d[9] ^ d[13] ^ d[21] ^ d[22] ^ d[23];
assign	c[30] = q[6] ^ q[12] ^ q[15] ^ q[16] ^ q[18] ^ q[22] ^ q[30] ^ q[31] ^ d[4] ^ d[7] ^ d[8] ^ d[10] ^ d[14] ^ d[22] ^ d[23];
assign	c[31] = q[7] ^ q[13] ^ q[16] ^ q[17] ^ q[19] ^ q[23] ^ q[31] ^ d[5] ^ d[8] ^ d[9] ^ d[11] ^ d[15] ^ d[23];

endmodule



module usb3_crc_dpp16 (

input 	wire	[15:0]	di,
input	wire	[31:0]	q,
output	wire	[31:0]	crc_out,
input	wire			rst,
input	wire			clk

);

wire [31:0]	c;
wire [15:0] d = {	di[0 ],di[1 ],di[2 ],di[3 ],di[4 ],di[5 ],di[6 ],di[7],
					di[8 ],di[9 ],di[10],di[11],di[12],di[13],di[14],di[15]};
						
assign crc_out = ~{	c[0],  c[1],  c[2],  c[3],  c[4],  c[5],  c[6],  c[7], 
					c[8],  c[9],  c[10], c[11], c[12], c[13], c[14], c[15],
					c[16], c[17], c[18], c[19], c[20], c[21], c[22], c[23], 
					c[24], c[25], c[26], c[27], c[28], c[29], c[30], c[31]};

assign	c[0] = q[16] ^ q[22] ^ q[25] ^ q[26] ^ q[28] ^ d[0] ^ d[6] ^ d[9] ^ d[10] ^ d[12];
assign	c[1] = q[16] ^ q[17] ^ q[22] ^ q[23] ^ q[25] ^ q[27] ^ q[28] ^ q[29] ^ d[0] ^ d[1] ^ d[6] ^ d[7] ^ d[9] ^ d[11] ^ d[12] ^ d[13];
assign	c[2] = q[16] ^ q[17] ^ q[18] ^ q[22] ^ q[23] ^ q[24] ^ q[25] ^ q[29] ^ q[30] ^ d[0] ^ d[1] ^ d[2] ^ d[6] ^ d[7] ^ d[8] ^ d[9] ^ d[13] ^ d[14];
assign	c[3] = q[17] ^ q[18] ^ q[19] ^ q[23] ^ q[24] ^ q[25] ^ q[26] ^ q[30] ^ q[31] ^ d[1] ^ d[2] ^ d[3] ^ d[7] ^ d[8] ^ d[9] ^ d[10] ^ d[14] ^ d[15];
assign	c[4] = q[16] ^ q[18] ^ q[19] ^ q[20] ^ q[22] ^ q[24] ^ q[27] ^ q[28] ^ q[31] ^ d[0] ^ d[2] ^ d[3] ^ d[4] ^ d[6] ^ d[8] ^ d[11] ^ d[12] ^ d[15];
assign	c[5] = q[16] ^ q[17] ^ q[19] ^ q[20] ^ q[21] ^ q[22] ^ q[23] ^ q[26] ^ q[29] ^ d[0] ^ d[1] ^ d[3] ^ d[4] ^ d[5] ^ d[6] ^ d[7] ^ d[10] ^ d[13];
assign	c[6] = q[17] ^ q[18] ^ q[20] ^ q[21] ^ q[22] ^ q[23] ^ q[24] ^ q[27] ^ q[30] ^ d[1] ^ d[2] ^ d[4] ^ d[5] ^ d[6] ^ d[7] ^ d[8] ^ d[11] ^ d[14];
assign	c[7] = q[16] ^ q[18] ^ q[19] ^ q[21] ^ q[23] ^ q[24] ^ q[26] ^ q[31] ^ d[0] ^ d[2] ^ d[3] ^ d[5] ^ d[7] ^ d[8] ^ d[10] ^ d[15];
assign	c[8] = q[16] ^ q[17] ^ q[19] ^ q[20] ^ q[24] ^ q[26] ^ q[27] ^ q[28] ^ d[0] ^ d[1] ^ d[3] ^ d[4] ^ d[8] ^ d[10] ^ d[11] ^ d[12];
assign	c[9] = q[17] ^ q[18] ^ q[20] ^ q[21] ^ q[25] ^ q[27] ^ q[28] ^ q[29] ^ d[1] ^ d[2] ^ d[4] ^ d[5] ^ d[9] ^ d[11] ^ d[12] ^ d[13];
assign	c[10] = q[16] ^ q[18] ^ q[19] ^ q[21] ^ q[25] ^ q[29] ^ q[30] ^ d[0] ^ d[2] ^ d[3] ^ d[5] ^ d[9] ^ d[13] ^ d[14];
assign	c[11] = q[16] ^ q[17] ^ q[19] ^ q[20] ^ q[25] ^ q[28] ^ q[30] ^ q[31] ^ d[0] ^ d[1] ^ d[3] ^ d[4] ^ d[9] ^ d[12] ^ d[14] ^ d[15];
assign	c[12] = q[16] ^ q[17] ^ q[18] ^ q[20] ^ q[21] ^ q[22] ^ q[25] ^ q[28] ^ q[29] ^ q[31] ^ d[0] ^ d[1] ^ d[2] ^ d[4] ^ d[5] ^ d[6] ^ d[9] ^ d[12] ^ d[13] ^ d[15];
assign	c[13] = q[17] ^ q[18] ^ q[19] ^ q[21] ^ q[22] ^ q[23] ^ q[26] ^ q[29] ^ q[30] ^ d[1] ^ d[2] ^ d[3] ^ d[5] ^ d[6] ^ d[7] ^ d[10] ^ d[13] ^ d[14];
assign	c[14] = q[18] ^ q[19] ^ q[20] ^ q[22] ^ q[23] ^ q[24] ^ q[27] ^ q[30] ^ q[31] ^ d[2] ^ d[3] ^ d[4] ^ d[6] ^ d[7] ^ d[8] ^ d[11] ^ d[14] ^ d[15];
assign	c[15] = q[19] ^ q[20] ^ q[21] ^ q[23] ^ q[24] ^ q[25] ^ q[28] ^ q[31] ^ d[3] ^ d[4] ^ d[5] ^ d[7] ^ d[8] ^ d[9] ^ d[12] ^ d[15];
assign	c[16] = q[0] ^ q[16] ^ q[20] ^ q[21] ^ q[24] ^ q[28] ^ q[29] ^ d[0] ^ d[4] ^ d[5] ^ d[8] ^ d[12] ^ d[13];
assign	c[17] = q[1] ^ q[17] ^ q[21] ^ q[22] ^ q[25] ^ q[29] ^ q[30] ^ d[1] ^ d[5] ^ d[6] ^ d[9] ^ d[13] ^ d[14];
assign	c[18] = q[2] ^ q[18] ^ q[22] ^ q[23] ^ q[26] ^ q[30] ^ q[31] ^ d[2] ^ d[6] ^ d[7] ^ d[10] ^ d[14] ^ d[15];
assign	c[19] = q[3] ^ q[19] ^ q[23] ^ q[24] ^ q[27] ^ q[31] ^ d[3] ^ d[7] ^ d[8] ^ d[11] ^ d[15];
assign	c[20] = q[4] ^ q[20] ^ q[24] ^ q[25] ^ q[28] ^ d[4] ^ d[8] ^ d[9] ^ d[12];
assign	c[21] = q[5] ^ q[21] ^ q[25] ^ q[26] ^ q[29] ^ d[5] ^ d[9] ^ d[10] ^ d[13];
assign	c[22] = q[6] ^ q[16] ^ q[25] ^ q[27] ^ q[28] ^ q[30] ^ d[0] ^ d[9] ^ d[11] ^ d[12] ^ d[14];
assign	c[23] = q[7] ^ q[16] ^ q[17] ^ q[22] ^ q[25] ^ q[29] ^ q[31] ^ d[0] ^ d[1] ^ d[6] ^ d[9] ^ d[13] ^ d[15];
assign	c[24] = q[8] ^ q[17] ^ q[18] ^ q[23] ^ q[26] ^ q[30] ^ d[1] ^ d[2] ^ d[7] ^ d[10] ^ d[14];
assign	c[25] = q[9] ^ q[18] ^ q[19] ^ q[24] ^ q[27] ^ q[31] ^ d[2] ^ d[3] ^ d[8] ^ d[11] ^ d[15];
assign	c[26] = q[10] ^ q[16] ^ q[19] ^ q[20] ^ q[22] ^ q[26] ^ d[0] ^ d[3] ^ d[4] ^ d[6] ^ d[10];
assign	c[27] = q[11] ^ q[17] ^ q[20] ^ q[21] ^ q[23] ^ q[27] ^ d[1] ^ d[4] ^ d[5] ^ d[7] ^ d[11];
assign	c[28] = q[12] ^ q[18] ^ q[21] ^ q[22] ^ q[24] ^ q[28] ^ d[2] ^ d[5] ^ d[6] ^ d[8] ^ d[12];
assign	c[29] = q[13] ^ q[19] ^ q[22] ^ q[23] ^ q[25] ^ q[29] ^ d[3] ^ d[6] ^ d[7] ^ d[9] ^ d[13];
assign	c[30] = q[14] ^ q[20] ^ q[23] ^ q[24] ^ q[26] ^ q[30] ^ d[4] ^ d[7] ^ d[8] ^ d[10] ^ d[14];
assign	c[31] = q[15] ^ q[21] ^ q[24] ^ q[25] ^ q[27] ^ q[31] ^ d[5] ^ d[8] ^ d[9] ^ d[11] ^ d[15];

endmodule


module usb3_crc_dpp8 (

input 	wire	[7:0]	di,
input	wire	[31:0]	q,
output	wire	[31:0]	crc_out,
input	wire			rst,
input	wire			clk

);

wire [31:0]	c;
wire [7:0] d = {	di[0 ],di[1 ],di[2 ],di[3 ],di[4 ],di[5 ],di[6 ],di[7]};
						
assign crc_out = ~{	c[0],  c[1],  c[2],  c[3],  c[4],  c[5],  c[6],  c[7], 
					c[8],  c[9],  c[10], c[11], c[12], c[13], c[14], c[15],
					c[16], c[17], c[18], c[19], c[20], c[21], c[22], c[23], 
					c[24], c[25], c[26], c[27], c[28], c[29], c[30], c[31]};

assign	c[0] = q[24] ^ q[30] ^ d[0] ^ d[6];
assign	c[1] = q[24] ^ q[25] ^ q[30] ^ q[31] ^ d[0] ^ d[1] ^ d[6] ^ d[7];
assign	c[2] = q[24] ^ q[25] ^ q[26] ^ q[30] ^ q[31] ^ d[0] ^ d[1] ^ d[2] ^ d[6] ^ d[7];
assign	c[3] = q[25] ^ q[26] ^ q[27] ^ q[31] ^ d[1] ^ d[2] ^ d[3] ^ d[7];
assign	c[4] = q[24] ^ q[26] ^ q[27] ^ q[28] ^ q[30] ^ d[0] ^ d[2] ^ d[3] ^ d[4] ^ d[6];
assign	c[5] = q[24] ^ q[25] ^ q[27] ^ q[28] ^ q[29] ^ q[30] ^ q[31] ^ d[0] ^ d[1] ^ d[3] ^ d[4] ^ d[5] ^ d[6] ^ d[7];
assign	c[6] = q[25] ^ q[26] ^ q[28] ^ q[29] ^ q[30] ^ q[31] ^ d[1] ^ d[2] ^ d[4] ^ d[5] ^ d[6] ^ d[7];
assign	c[7] = q[24] ^ q[26] ^ q[27] ^ q[29] ^ q[31] ^ d[0] ^ d[2] ^ d[3] ^ d[5] ^ d[7];
assign	c[8] = q[0] ^ q[24] ^ q[25] ^ q[27] ^ q[28] ^ d[0] ^ d[1] ^ d[3] ^ d[4];
assign	c[9] = q[1] ^ q[25] ^ q[26] ^ q[28] ^ q[29] ^ d[1] ^ d[2] ^ d[4] ^ d[5];
assign	c[10] = q[2] ^ q[24] ^ q[26] ^ q[27] ^ q[29] ^ d[0] ^ d[2] ^ d[3] ^ d[5];
assign	c[11] = q[3] ^ q[24] ^ q[25] ^ q[27] ^ q[28] ^ d[0] ^ d[1] ^ d[3] ^ d[4];
assign	c[12] = q[4] ^ q[24] ^ q[25] ^ q[26] ^ q[28] ^ q[29] ^ q[30] ^ d[0] ^ d[1] ^ d[2] ^ d[4] ^ d[5] ^ d[6];
assign	c[13] = q[5] ^ q[25] ^ q[26] ^ q[27] ^ q[29] ^ q[30] ^ q[31] ^ d[1] ^ d[2] ^ d[3] ^ d[5] ^ d[6] ^ d[7];
assign	c[14] = q[6] ^ q[26] ^ q[27] ^ q[28] ^ q[30] ^ q[31] ^ d[2] ^ d[3] ^ d[4] ^ d[6] ^ d[7];
assign	c[15] = q[7] ^ q[27] ^ q[28] ^ q[29] ^ q[31] ^ d[3] ^ d[4] ^ d[5] ^ d[7];
assign	c[16] = q[8] ^ q[24] ^ q[28] ^ q[29] ^ d[0] ^ d[4] ^ d[5];
assign	c[17] = q[9] ^ q[25] ^ q[29] ^ q[30] ^ d[1] ^ d[5] ^ d[6];
assign	c[18] = q[10] ^ q[26] ^ q[30] ^ q[31] ^ d[2] ^ d[6] ^ d[7];
assign	c[19] = q[11] ^ q[27] ^ q[31] ^ d[3] ^ d[7];
assign	c[20] = q[12] ^ q[28] ^ d[4];
assign	c[21] = q[13] ^ q[29] ^ d[5];
assign	c[22] = q[14] ^ q[24] ^ d[0];
assign	c[23] = q[15] ^ q[24] ^ q[25] ^ q[30] ^ d[0] ^ d[1] ^ d[6];
assign	c[24] = q[16] ^ q[25] ^ q[26] ^ q[31] ^ d[1] ^ d[2] ^ d[7];
assign	c[25] = q[17] ^ q[26] ^ q[27] ^ d[2] ^ d[3];
assign	c[26] = q[18] ^ q[24] ^ q[27] ^ q[28] ^ q[30] ^ d[0] ^ d[3] ^ d[4] ^ d[6];
assign	c[27] = q[19] ^ q[25] ^ q[28] ^ q[29] ^ q[31] ^ d[1] ^ d[4] ^ d[5] ^ d[7];
assign	c[28] = q[20] ^ q[26] ^ q[29] ^ q[30] ^ d[2] ^ d[5] ^ d[6];
assign	c[29] = q[21] ^ q[27] ^ q[30] ^ q[31] ^ d[3] ^ d[6] ^ d[7];
assign	c[30] = q[22] ^ q[28] ^ q[31] ^ d[4] ^ d[7];
assign	c[31] = q[23] ^ q[29] ^ d[5];
	
endmodule
